JJ80901/GSP-Motion-Board-Rev.-C/Simulations/USB & Battery Switch.asc

D1: schottky
M1: pmos; DMP2045U
R1: Res; 100k
V1: voltage; PULSE(5 0 5 1n 1n 5 5)
V2: voltage; 3.7
Named nets: 0, Out
.tran 10
.include "C:/Users/jj/Documents/KiCad/8.0/projects/GSP RevC/Simulations/DMP2045U.lib"
